pigatron-industries/xen_midi2cv/src/drivers/GateOutput.h

#ifndef GateOutput_h
#define GateOutput_h

#include <inttypes.h>
#include "../lib/io/Timer.h"

#define CLOCKINTERVAL 1 //us
#define TRIGGER_TIME 4000 //us

class GateOutput {

public:
    GateOutput(uint8_t dataPin, uint8_t latchPin, uint8_t clockPin, uint8_t size);

    void setValue(uint8_t index, bool value);
    void setTrigger(uint8_t index);
    void update();
    void sendData();

    uint8_t getSize() { return _size; };
    bool* getData() { return _data; };

private:
    uint8_t _dataPin;
    uint8_t _latchPin;
    uint8_t _clockPin;
    uint8_t _size;

    bool* _data;

    Timer* _triggerTimer;

};

#endif
