pigatron-industries/xen_midi2cv/src/drivers/CvOutputService.cpp

#include "CvOutputService.h"

#include "../hwconfig.h"

CvOutputService::CvOutputService(Configuration& config, GateOutput& gateOutput,
                                 PitchCvOutput& pitchCvOutput, CvOutput& cvOutput) :
        _config(config),
        _gateOutput(gateOutput),
        _pitchCvOutput(pitchCvOutput),
        _cvOutput(cvOutput) {
}

void CvOutputService::update() {
     _gateOutput.update();
     _gateOutput.sendData();
     _pitchCvOutput.sendData();
}

void CvOutputService::setPitchValue(int8_t index, float value) {
    _pitchCvOutput.setVoltage(index, value);
}


void CvOutputService::setGateValue(int8_t channel, int8_t bank, bool value) {
    _gateOutput.setValue(getIndex(channel, bank), value);
}


void CvOutputService::setTrigger(int8_t channel, int8_t bank) {
    _gateOutput.setTrigger(getIndex(channel, bank));
}


void CvOutputService::setControlValue(int8_t channel, int8_t bank, float value) {
    _cvOutput.setVoltage(getIndex(channel, bank), value);
}

int8_t CvOutputService::getIndex(int8_t channel, int8_t bank) {
    return (bank * CV_CHANNELS) + channel;
}
