pigatron-industries/xen_midi2cv/src/programs/midi/MidiToPitchConverter.h

#ifndef MidiToPitchConverter_h
#define MidiToPitchConverter_h

#include "../../config/Configuration.h"

#include <inttypes.h>

class MidiToPitchConverter {

public:
    MidiToPitchConverter(Configuration& config);

    float convertNote(int8_t note);
    float convertBend(int16_t bend);
    float convertVelocity(uint8_t velocity);
    float convertControl(uint16_t value);

private:
    Configuration& _config;

};


#endif
